smcameron/snis-consoles/src/models/nav-2x2-large-switch-array-holder.scad

rows=2;
cols=2;

include <large-switch-array-holder.scad>

switch_array_holder(rows, cols);
