smcameron/snis-consoles/src/models/nav-2x2-switch-retaining-gasket.scad

rows=2;
cols=2;

include <large-switch-array-holder.scad>

switch_holder_retaining_gasket(rows, cols);
