smcameron/snis-consoles/src/models/nav-2x5-large-switch-array-holder.scad

rows=5;
cols=2;

include <large-switch-array-holder.scad>
