smcameron/snis-consoles/src/models/nav-2x5-switch-retaining-gasket.scad

rows=5;
cols=2;

include <large-switch-array-holder.scad>

switch_holder_retaining_gasket(rows, cols);
