smcameron/snis-consoles/src/models/nav-5x1-large-switch-array-holder.scad

rows=1;
cols=5;

include <large-switch-array-holder.scad>
