smcameron/snis-consoles/src/models/nav-5x1-switch-retaining-gasket.scad

rows=1;
cols=5;

include <large-switch-array-holder.scad>

switch_holder_retaining_gasket(rows, cols);
