smcameron/snis-consoles/src/models/nav-5x4-large-switch-array-holder.scad

rows=4;
cols=5;

include <large-switch-array-holder.scad>
