smcameron/snis-consoles/src/models/nav-impulse-warp-fader-insert.scad

/*
  3d printable insert for warp and impulse faders on Navigation control panel
*/

plate_thickness = 3;
countersink = 0.01;
fader_spacing = 40;
fader_count = 2;
web_thickness = 3;
web_height = 10;
tang_hole_width = 2;
plate_height = 120;
fader_screw_holes = 0; /* no fader holes */
use_fader_snap_arms = 1;
fader_phys_length = 88.5; /* extra half millimeter for tolerance */
fader_phys_width = 12.5;
fader_snap_arm_count = 4;
side_margin = 0.5 * fader_spacing;

include <fader-insert-60mm-array.scad>

fader_60mm_array_insert(0, 0, fader_spacing, fader_count);
